shashfrankenstien/ArchieTiny/src/drivers/sh1106.asm

; this program interfaces with SH1106 OLED display over i2c

.equ OLED_ADDR,                 0b00111100              ; 0x3c
.equ OLED_WRITE_ADDR,           (OLED_ADDR << 1) | 0x00 ; 0x78
.equ OLED_READ_ADDR,            (OLED_ADDR << 1) | 0x01 ; 0x79

; control byte                                          ; if bit 8 is set, we can send 1 data byte after this
.equ OLED_WRITE_DATA,           0b11000000              ; if bit 7 is set, indicates that the next byte needs to be stored in memory
.equ OLED_WRITE_CMD,            0b10000000              ; if bit 7 is clear, the next byte will be a command

.equ OLED_WRITE_DATA_LIST,      0b01000000
.equ OLED_WRITE_CMD_LIST,       0b00000000

.equ OLED_READ_MOD_WRITE_START, 0xe0                    ; commands for read-modify-write operation
.equ OLED_READ_MOD_WRITE_END,   0xee                    ; see page 28 of sh1106 data sheet

; commands
.equ SET_DISPLY_OFF,         0xae                    ; 0b1010111x
.equ SET_DISPLY_ON,          0xaf                    ; where x is 1 for ON and 0 for OFF

.equ SET_PAGE_ADDRESS,       0xb0                    ; 0b10110xxx where xxx are page addresses 0 - 7
.equ SET_COLUMN_L,           0x00                    ; 0b0000xxxx where xxxx are column number low bits
.equ SET_COLUMN_H,           0x10                    ; 0b0001xxxx where xxxx are column number high bits

.equ SET_DISP_FREQ_MODE,     0xd5                    ; double command. use with DEFAULT_DISP_FREQ
.equ DEFAULT_DISP_FREQ,      0x50

.equ SET_COLOR_NORM,         0xa6                    ; normal = white fg, black bg
.equ SET_COLOR_INV,          0xa7                    ; inverted = black fg, white bg

.equ SET_COMM_SCAN_DIR_NORM, 0xc0                    ; normal = page numbers start on the end away from the i2c pinout
.equ SET_COMM_SCAN_DIR_INV,  0xc8                    ; inverted = page numbers start on the end closer to the i2c pinout

.equ SET_SEGMENT_REMAP_NORM, 0xa0                    ; column scanning direction left to right or right to left
.equ SET_SEGMENT_REMAP_INV,  0xa1                    ; reverse of SET_SEGMENT_REMAP_NORM

.equ SET_DISPLY_LINE_OFFSET, 0xd3                    ; set display offset (double byte command) - followed by a number betwee 0 - 63

.equ SET_DISPLY_START_LINE,  0x40                    ; set display start line: (0x40 - 0x7f) - ORed with a number betwee 0 - 63


.equ SET_CONTRAST_CMD,      0x81                     ; set contrast (double byte command) - followed by a number betwee 0 - 255



; SREG_OLED - oled status register (1)
;   - register holds 8 oled status flags
;      --------------------------------------------------------------------------------------------------------------
;      |  CNTRST3  |  CNTRST2  |  CNTRST1  |  CNTRST0  |  OLED_COLOR_INVERT  |  SCRL_PG2  |  SCRL_PG1  |  SCRL_PG0  |
;      --------------------------------------------------------------------------------------------------------------
;
; SCRL_PG[2:0] - display scroll page (bits 2:0)
;   - this is a 3 bit number indicating current page scroll position on the screen (0 - 7)
;   - text scrolling is performed 8 rows (1 page) at a time
;   - oled_set_cursor routine can use this to normalize column and row indexing to the user
;
; OLED_COLOR_INVERT (bit 3)
;   - this flag is used to implement software color inverted mode
;   - NOTE: this is different from SET_COLOR_INV, which is an oled device function to invert the entire screen
;   - if OLED_COLOR_INVERT is set, anything written through the oled routines will be inverted (1's complement using COM instruction)
;       if OLED_COLOR_INVERT is cleared, it writes without 1's complement
.equ    OLED_COLOR_INVERT,       3
;
; OLED contrast level - SREG_OLED[7:4] (CNTRST[3:0])
;   - location to store current contrast level set by oled_set_contrast

;
; --------------------------------------------------
.equ    OLED_MAX_COL,            127                        ; max column index (128 x 64)
.equ    OLED_MAX_PAGE,           7                          ; max page index (each page has 8 rows)
.equ    OLED_MAX_ROWS,           ((OLED_MAX_PAGE + 1) * 8)  ; each page has 8 rows. OLED_MAX_ROWS = number of pages * 8
; --------------------------------------------------


; initialize oled and set default settings
oled_init:
    push r16

    clr r16
    sts SREG_OLED, r16                         ; clear oled status register

    rcall i2c_do_stop_condition                ; call stop condition just in case (mostly not required)

    rcall oled_io_open_write_cmds

    ldi r16, SET_DISPLY_OFF                    ; turn on the display
    rcall i2c_send_byte
    ldi r16, SET_DISP_FREQ_MODE                ; set the display refresh rate (double command)
    rcall i2c_send_byte
    ldi r16, DEFAULT_DISP_FREQ
    rcall i2c_send_byte

    ; ; rotate oled 180 degrees by flipping both column and page scan directions
    ; ldi r16, SET_COMM_SCAN_DIR_INV             ; flip the screen
    ; rcall i2c_send_byte
    ; ldi r16, SET_SEGMENT_REMAP_INV             ; reverse the column scan direction
    ; rcall i2c_send_byte

    ldi r16, SET_DISPLY_LINE_OFFSET            ; set offset (different from scroll?)
    rcall i2c_send_byte
    ldi r16, 0
    rcall i2c_send_byte
    ldi r16, SET_DISPLY_START_LINE | 0         ; set scroll state to 0
    rcall i2c_send_byte

    ldi r16, SET_DISPLY_ON                     ; turn on the display
    rcall i2c_send_byte

    rcall oled_io_close
    rcall oled_clr_screen

    ldi r16, 5                                 ; default contrast = 5 (possible values 0 - 15)
    rcall oled_set_contrast

    pop r16
    ret



; ----------------- i2c IO wrappers ---------------

; use this routine to start a command list write transaction
; this routine modifies r16 so that it contains ACK in LSB
oled_io_open_write_cmds:
    rcall i2c_do_start_condition

    ldi r16, OLED_WRITE_ADDR                   ; i2c communication always starts with the address + read/write flag
    rcall i2c_send_byte

    ldi r16, OLED_WRITE_CMD_LIST               ; this control byte tells the display to expect a list of commands until stop condition
    rcall i2c_send_byte
    ret                                        ; return value r16 will contain ACK from last byte transfered


; use this routine to start a data list write transaction
; this routine modifies r16 so that it contains ACK in LSB
oled_io_open_write_data:
    rcall i2c_do_start_condition

    ldi r16, OLED_WRITE_ADDR                   ; i2c communication always starts with the address + read/write flag
    rcall i2c_send_byte

    ldi r16, OLED_WRITE_DATA_LIST              ; this tells the device to expect a list of data bytes until stop condition
    rcall i2c_send_byte
    ret                                        ; return value r16 will contain ACK from last byte transfered


; use this routine to start a data read transaction
; this routine modifies r16 so that it contains ACK in LSB
oled_io_open_read_data:
    rcall i2c_do_start_condition

    ldi r16, OLED_WRITE_ADDR                   ; oled retains the previous control byte indicating command or data
    rcall i2c_send_byte                        ; if command (OLED_WRITE_CMD - ex: setting the cursor), then the data read back will be the oled status flag
    ldi r16, OLED_WRITE_DATA                   ; so, first we need to write the command byte indicating we want to access data (OLED_WRITE_DATA)
    rcall i2c_send_byte

    rcall i2c_do_start_condition               ; then, we send a restart event after which we will be able to read display RAM data

    ldi r16, OLED_READ_ADDR                    ; i2c communication to read
    rcall i2c_send_byte

    rcall i2c_read_byte_ack                    ; perform dummy read per sh1106 docs
    ret


oled_io_close:
    rcall i2c_do_stop_condition
    ret



; ----------------- read-modify-write wrappers ---------------

oled_read_mod_write_start:
    rcall i2c_do_start_condition

    ldi r16, OLED_WRITE_ADDR                   ; i2c communication always starts with the address + read/write flag
    rcall i2c_send_byte

    ldi r16, OLED_WRITE_CMD
    rcall i2c_send_byte

    ldi r16, OLED_READ_MOD_WRITE_START
    rcall i2c_send_byte

    rcall i2c_do_stop_condition

    ret



oled_read_mod_write_end:
    rcall i2c_do_start_condition

    ldi r16, OLED_WRITE_ADDR                   ; i2c communication always starts with the address + read/write flag
    rcall i2c_send_byte

    ldi r16, OLED_WRITE_CMD
    rcall i2c_send_byte

    ldi r16, OLED_READ_MOD_WRITE_END
    rcall i2c_send_byte

    rcall i2c_do_stop_condition
    ret



; -------------- SREG_OLED wrappers ----------------

oled_color_inv_start:
    push r16
    lds r16, SREG_OLED
    sbr r16, (1 << OLED_COLOR_INVERT)        ; set to invert color
    sts SREG_OLED, r16
    pop r16
    ret


oled_color_inv_stop:
    push r16
    lds r16, SREG_OLED
    cbr r16, (1 << OLED_COLOR_INVERT)        ; set to normal color
    sts SREG_OLED, r16
    pop r16
    ret
; -------------------------------------------------



; oled_set_cursor takes
;   - r16 - page address
;   - r17 - column address
; performs set page and set column address operations
oled_set_cursor:
    .irp param,16,17,18,19
        push r\param
    .endr
    mov r19, r16                               ; store page number for later

    inc r17
    inc r17                                    ; screen is somehow offset by 2 columns ?? :/
                                               ; In SH1106 driver, 128x64 OLED is centered within the 132x64 ram,
                                               ;    that means pixel (2,0) in ram is pixel (0,0) on the display
    mov r18, r17
    swap r18
    andi r18, 0x0f                             ; keep high nibble of column address by swapping nibbles + andi 0x0f
    ori r18, SET_COLUMN_H                      ; set column start addr high nibble

    andi r17, 0x0f                             ; keep low nibble of column address
    ori r17, SET_COLUMN_L                      ; set column start addr low nibble

    rcall oled_io_open_write_cmds

    mov r16, r19                               ; get required page number
    ori r16, SET_PAGE_ADDRESS                  ; OR with SET_PAGE_ADDRESS cmd
    rcall i2c_send_byte

    ; set cursor to precomputed column low and high commands saved in r17 and r18
    mov r16, r17
    rcall i2c_send_byte
    mov r16, r18
    rcall i2c_send_byte

    rcall oled_io_close

    .irp param,19,18,17,16
        pop r\param
    .endr
    ret


; oled_set_relative_cursor takes
;   - r16 - page address
;   - r17 - column address
; performs set page and set column address operations
; not affected by current page scroll position SCRL_PG[2:0] in SREG_OLED
oled_set_relative_cursor:
    push r16
    push r18

    lds r18, SREG_OLED                         ; load SREG_OLED and get current scroll position
    add r16, r18                               ; relative page scroll position = (cur + req) & 0b00000111
    andi r16, 0b00000111
    rcall oled_set_cursor

    pop r18
    pop r16
    ret



; scrolls screen down by 8 rows since a page is 8 rows high (1 page)
; this method wipes the top row first before scrolling, leaving a new blank line at the bottom
oled_scroll_page_down:
    push r16
    push r17

    ; wipe top row
    clr r16
    clr r17
    rcall oled_wipe_eol

    ; perform scroll
    lds r16, SREG_OLED                         ; load SREG_OLED and get current scroll position
    mov r17, r16
    inc r16
    andi r16, 0b00000111                       ; keep only lower 3 bits in case of overflow (0 - 7)

    andi r17, 0b11111000                       ; keep higher 5 bits from current SREG_OLED
    or r17, r16
    sts SREG_OLED, r17                         ; update SREG_OLED with new scroll position

    ldi r17, 8
    rcall mul8                                 ; multiply r16 by 8 to get scroll position in rows (0 - 63). LSB of result is returned in r16
    andi r16, 0b00111111                       ; keep only lower 6 bits in case of overflow (0 - 63)
    mov r17, r16                               ; save new scroll position in r17

    rcall oled_io_open_write_cmds
    mov r16, r17                               ; reload r16 as oled_io_open_write_cmds modifies this register
    ori r16, SET_DISPLY_START_LINE
    rcall i2c_send_byte
    rcall oled_io_close

    pop r17
    pop r16
    ret



; scrolls screen up by 8 rows since a page is 8 rows high (1 page)
; this method wipes the bottom row first before scrolling, leaving a new blank line at the top
oled_scroll_page_up:
    push r16
    push r17

    ; wipe bottom row
    ldi r16, OLED_MAX_PAGE
    clr r17
    rcall oled_wipe_eol

    ; perform scroll
    lds r16, SREG_OLED                         ; load SREG_OLED and get current scroll position
    mov r17, r16
    dec r16
    andi r16, 0b00000111                       ; keep only lower 3 bits in case of overflow (0 - 7)

    andi r17, 0b11111000                       ; keep higher 5 bits from current SREG_OLED
    or r17, r16
    sts SREG_OLED, r17                         ; update SREG_OLED with new scroll position

    ldi r17, 8
    rcall mul8                                 ; multiply r16 by 8 to get scroll position in rows (0 - 63). LSB of result is returned in r16
    andi r16, 0b00111111                       ; keep only lower 6 bits in case of overflow (0 - 63)
    mov r17, r16                               ; save new scroll position in r17

    rcall oled_io_open_write_cmds
    mov r16, r17                               ; reload r16 as oled_io_open_write_cmds modifies this register
    ori r16, SET_DISPLY_START_LINE
    rcall i2c_send_byte
    rcall oled_io_close

    pop r17
    pop r16
    ret


; resets oled scroll position
oled_scroll_page_reset:
    push r16

    lds r16, SREG_OLED                         ; load SREG_OLED and get current scroll position
    cbr r16, 0b00000111                        ; set scroll position to 0
    sts SREG_OLED, r16                         ; update SREG_OLED

    rcall oled_io_open_write_cmds
    ldi r16, SET_DISPLY_START_LINE | 0         ; set scroll position to 0
    rcall i2c_send_byte
    rcall oled_io_close

    pop r16
    ret


; oled_set_contrast takes contrast value in r16
;   - this routine scales the value down to 16 steps (takes 0 to 15 in r16)
oled_set_contrast:
    push r16
    push r17

    andi r16, 0b00001111                        ; only keep low 4 bits (0 to 15)

    lds r17, SREG_OLED                          ; read current SREG_OLED
    andi r17, 0b00001111                        ; only keep low 4 bits and update high 4 bits with contrast value
    swap r17
    or r17, r16
    swap r17
    sts SREG_OLED, r17                          ; update SREG_OLED

    ldi r17, 16
    rcall mul8                                  ; scale up: 0 to 15 => 0 to 255

    cpi r16, 1                                  ; minimum allowed value is 1 (this will be used if output value is 0)
    brsh _oled_set_contrast_ok
    ldi r16, 1
_oled_set_contrast_ok:
    push r16
    rcall oled_io_open_write_cmds
    ldi r16, SET_CONTRAST_CMD
    rcall i2c_send_byte
    pop r16
    rcall i2c_send_byte
    rcall oled_io_close

    pop r17
    pop r16
    ret

; -------------------------------------------------

; write all zeros onto oled
; also reset scroll position
oled_clr_screen:
    .irp param,16,17,18,19,20
        push r\param
    .endr

    clr r16                                    ; fill byte = 0x00 (all 0s)
    clr r17                                    ; x1 = 0
    ldi r18, OLED_MAX_COL                      ; x2 = OLED_MAX_COL
    clr r19                                    ; y2 = 0
    ldi r20, OLED_MAX_ROWS                     ; y2 = OLED_MAX_ROWS (64 on the regular oled)
    rcall oled_fill_rect              ; fill oled with data in r16

    rcall oled_scroll_page_reset               ; reset scroll position

    .irp param,20,19,18,17,16
        pop r\param
    .endr
    ret



; 'oled_wipe_eol' takes
;   - r16 - page address
;   - r17 - column address
; sets the cursor to the required location
; writes 0s till end of line from current column (r17)
; returns after resetting the cursor to the right location
oled_wipe_eol:
    push r16
    push r17

    rcall oled_set_relative_cursor             ; set cursor initially
    rcall oled_io_open_write_data

_next_wipe_column:
    clr r16
    rcall i2c_send_byte                        ; i2c_send_byte modifies r16, so we need to reload r16 at every iteration
    inc r17
    cpi r17, OLED_MAX_COL + 1
    brne _next_wipe_column

    rcall oled_io_close                        ; finished writing a page

    pop r17
    pop r16
    rcall oled_set_relative_cursor             ; finally set cursor to desired page (r16) and column (r17)
    ret


; --------------------------------------------------


; oled_fill_page_row takes 3 coordinates - x1, x2, y
; it will fill page y between x1 and x2 columns with the fill byte in r16
; input registers -
;   r16 - byte to fill
;   r17 - x1
;   r18 - x2
;   r19 - y         ; row (page) address 0 to 7
oled_fill_page_row:
    .irp param,17,18,19,20
        push r\param
    .endr

    inc r18                                    ; increment x2 so that we can break the loop once x1 overflows original x2
    mov r20, r16                               ; save away page fill byte till later because we need r16 for other stuff
    mov r16, r19
    rcall oled_set_cursor                      ; set cursor to start writing data

    rcall oled_io_open_write_data
_fill_page_next_column:                                  ; iterate columns x1 to x2
    mov r16, r20                               ; load back the fill byte that was originally saved away
    rcall i2c_send_byte                        ; i2c_send_byte modifies r16, so we need to reload r16 at every iteration
    inc r17
    cp r17, r18
    brne _fill_page_next_column

    rcall oled_io_close                        ; finished writing a page

    .irp param,20,19,18,17
        pop r\param
    .endr
    ret                                        ; return value r16 will contain ACK from last byte transfered



; oled_invert_inplace_relative_page_row takes 3 coordinates - x1, x2, y
; it will invert all bytes of page y between x1 and x2 columns
; input registers follow oled_fill_page_row convention -
;   r17 - x1
;   r18 - x2
;   r19 - y         ; row (page) address 0 to 7
oled_invert_inplace_relative_page_row:
    .irp param,16,17,18,19,20
        push r\param
    .endr

    inc r18                                    ; increment x2 so that we can break the loop once x1 overflows original x2
    mov r16, r19
    rcall oled_set_relative_cursor             ; set cursor to start writing data

    rcall oled_read_mod_write_start
_invert_inplace_next_column:
    rcall oled_io_open_read_data
    rcall i2c_read_byte_nack
    mov r20, r16
    rcall oled_io_close

    rcall oled_io_open_write_data
    mov r16, r20
    com r16
    rcall i2c_send_byte
    rcall oled_io_close
    inc r17
    cp r17, r18
    brne _invert_inplace_next_column

    rcall oled_read_mod_write_end

    .irp param,20,19,18,17,16
        pop r\param
    .endr
    ret






; oled_fill_rect takes 4 coordinates - x1, x2, y1, y2
; it will fill the rectangle between (x1,y1) (x1,y2) (x2,y1) (x2,y2)
; input registers -
;   r16 - byte to fill
;   r17 - x1
;   r18 - x2
;   r19 - y1
;   r20 - y2
;
; so
;   x1 and x2 indicate column addresses
;   y1 and y2 indicate actual row addresses between 0 and 63 (pixel resolution)
;
; handling y axis - convert 0 - 63 into page addr (0 - 7) and bit addr (0 - 7)
;   - this can be done by dividing the y value by 8. quotient will be page addr and remainder will be bit addr
;
; first, we will fill the pages associated with y1 and y2 with corresponding bit addr masked fill byte
; then, we will check if there are pages between y1 and y2 that needs filling, and fill those with the raw fill byte
oled_fill_rect:                               ; fill rect on screen with value in r16
                                               ; r16 through r20 are inputs. calling routine should push and pop these
    push r22
    push r23
    push r24
    push r25

    ; pre calc some stuff
    mov r22, r16                               ; save away page fill byte till later because we need r16 for other stuff
    lds r16, SREG_OLED
    sbrc r16, OLED_COLOR_INVERT                ; check if needs to be inverted
    com r22                                    ; invert!

    mov r23, r17                               ; save away x1 as we need r17 for div8

    ;  ------------------ deal with y1 -----------------------
    mov r16, r19
    ldi r17, 8
    rcall div8
    mov r19, r16                               ; move y1 page number into r19
    mov r16, r22                               ; load back the fill byte that was originally saved away

    tst r17
    breq _rect_page_0_fill_mask_done

    clc                                        ; clear carry flag
    ldi r24, 0xff
_rect_page_0_fill_mask:
    rol r24                                    ; bring in carry to bit 0
    and r16, r24                               ; knock off one LSB at a time using rol+and
    dec r17
    brne _rect_page_0_fill_mask

_rect_page_0_fill_mask_done:
    mov r17, r23                               ; load back x1
    rcall oled_fill_page_row
    mov r25, r19                               ; save away y1 page number for later

    ;  ------------------ deal with y2 -----------------------
    mov r16, r20
    ldi r17, 8
    rcall div8
    mov r19, r16                               ; move y2 page number into r19

    tst r17
    breq _rect_page_n_done

    ldi r16, 8
    sub r16, r17
    mov r17, r16

    mov r16, r22                               ; load back the fill byte that was originally saved away
    clc                                        ; clear carry flag
    ldi r24, 0xff
_rect_page_n_fill_mask:
    ror r24                                    ; bring in carry to bit 7
    and r16, r24                               ; knock off one MSB at a time using ror+and
    dec r17
    brne _rect_page_n_fill_mask

    mov r17, r23                               ; load back x1
    rcall oled_fill_page_row

_rect_page_n_done:
    mov r20, r19                               ; put y2 page number in r20
    mov r19, r25                               ; put y1 page number in r19
    ; ------------------------------------------------------------

    sub r20, r19                               ; subtract y1 from y2. if result is same or higher than 2, we need to fill intermediate pages
    cpi r20, 2
    brlo _rect_done

    dec r20                                    ; iterator for intermediate pages
    inc r19                                    ; start from the second page since first one is already handled (y1)

_rect_next_page2:                              ; iterate intermediate pages
    mov r16, r22                               ; load back the fill byte that was originally saved away
    rcall oled_fill_page_row
    inc r19
    dec r20
    brne _rect_next_page2

_rect_done:
    pop r25
    pop r24
    pop r23
    pop r22                                    ; r16 through r20 are inputs. calling routine should push and pop these
    ret                                        ; return value r16 will contain ACK from last byte transfered




; oled_draw_h_line_overlay takes 2 coordinates - x1, x2 and y
; it will draw a vertical line between x1 and x2 on row y
; input registers follow oled_fill_rect convention -
;   r16 - y
;   r17 - x1
;   r18 - x2
oled_draw_h_line_overlay:                      ; draw a horizontal line on screen without distorting existing pixels (*much)
    .irp param,16,17,18,19,20,21
        push r\param
    .endr

    mov r19, r16
    mov r20, r17

    ldi r17, 8
    rcall div8
    mov r21, r17
    mov r17, r20

    sec                                        ; set carry flag
    clr r20
    inc r21                                    ; increment r21 so that we can break once it reaches 0
_draw_h_line_bit_mask:
    rol r20                                    ; rotate in carry bit
    dec r21
    brne _draw_h_line_bit_mask

    rcall oled_set_relative_cursor
    rcall oled_read_mod_write_start
_draw_h_line_next_column:
    rcall oled_io_open_read_data
    rcall i2c_read_byte_nack
    mov r21, r16
    rcall oled_io_close

    or r21, r20

    rcall oled_io_open_write_data
    mov r16, r21
    rcall i2c_send_byte
    rcall oled_io_close
    inc r17
    cp r17, r18
    brne _draw_h_line_next_column

    rcall oled_read_mod_write_end

    .irp param,21,20,19,18,17,16
        pop r\param
    .endr
    ret


; ; oled_draw_line_overlay takes 4 coordinates - x1, x2, y1, y2
; ; it will fill the rectangle between (x1,y1) (x1,y2) (x2,y1) (x2,y2)
; ; input registers follow oled_fill_rect convention -
; ;   r17 - x1
; ;   r18 - x2
; ;   r19 - y1
; ;   r20 - y2
; ;
; oled_draw_line_overlay:               ; draw a line on screen without distorting existing pixels (*much)

;     mov r21, r20
;     sub r21, r19                              ; r21 = y2 - y1

;     mov r22, r18
;     sub r22, r17                              ; r22 = x2 - x1

;     mov r16, r21
;     mov r21, r17
;     mov r17, r22
;     rcall div8                                ; r16 (quotient), r17 (remainder) => (y2 - y1) / (x2 - x1). aka 'm' or slope

; --------------------------------------------------



; oled_io_put_char depends on a font being included. it will expect
;   - a label 'font_lut' that contains the lookup table for characters
;   - FONT_WIDTH constant which indicates how many bytes need to be written per character
;   - FONT_OFFSET constant which indicates the first ascii charater in the lookup table
;           consequent characters can be reached by incrementing by FONT_WIDTH
;
; it take one character ascii value in r16
; to write the character, we need to find the index of the character in font_lut
;   - index = addr of font_lut + ((r16 - FONT_OFFSET) * FONT_WIDTH)
;
; oled_io_put_char assumes that start condition has been signaled and cursor address is set before being called
; it also expects that the oled is in OLED_WRITE_DATA_LIST mode
; - these conditions can be met by just calling oled_io_open_write_data before, and oled_io_close after oled_io_put_char
oled_io_put_char:
    .irp param,17,18,19,30,31
        push r\param
    .endr
    in r19, SREG
    lds r18, SREG_OLED

    ldi r31, hi8(font_lut)          ; initialize Z-pointer to the start of the font lookup table
    ldi r30, lo8(font_lut)

    subi r16, FONT_OFFSET           ; (r16 - FONT_OFFSET) * FONT_WIDTH
    ldi r17, FONT_WIDTH
    rcall mul8                      ; output is stored in r17:r16 (character index)

    add r30, r16                    ; add the character index to Z pointer
    adc r31, r17                    ; add the character index to Z pointer

    ldi r17, FONT_WIDTH             ; load loop counter
_oled_io_put_char_next_byte:
    lpm r16, Z+                     ; load constant from flash
                                    ; memory pointed to by Z (r31:r30)
    sbrc r18, OLED_COLOR_INVERT     ; check if needs to be inverted
    com r16                         ; invert!
    rcall i2c_send_byte
    dec r17
    brne _oled_io_put_char_next_byte

    out SREG, r19
    .irp param,31,30,19,18,17
        pop r\param
    .endr
    ret                             ; return value r16 will contain ACK from last byte transfered




; oled_io_put_icon depends on a custom icon set being included. it will expect
;   - a label 'icon_lut' that contains the lookup table for icons
;   - ICON_WIDTH constant which indicates how many bytes need to be written per icon
;           consequent icons can be reached by incrementing by ICON_WIDTH
;
; it take one icon value in r16
; to write the icon, we need to find the index of the icon in icon_lut
;   - index = addr of icon_lut + (r16 * ICON_WIDTH)
;
; oled_io_put_icon assumes that start condition has been signaled and cursor address is set before being called
; it also expects that the oled is in OLED_WRITE_DATA_LIST mode
; - these conditions can be met by just calling oled_io_open_write_data before, and oled_io_close after oled_io_put_icon
oled_io_put_icon:
    .irp param,17,18,19,30,31
        push r\param
    .endr
    in r19, SREG
    lds r18, SREG_OLED

    ldi r31, hi8(icon_lut)          ; initialize Z-pointer to the start of the icon lookup table
    ldi r30, lo8(icon_lut)

    ldi r17, ICON_WIDTH             ; r16 * ICON_WIDTH
    rcall mul8                      ; output is stored in r17:r16 (icon index)

    add r30, r16                    ; add the icon index to Z pointer
    adc r31, r17                    ; add the icon index to Z pointer

    ldi r17, ICON_WIDTH             ; load loop counter
_oled_io_put_icon_next_byte:
    lpm r16, Z+                     ; load constant from flash
                                    ; memory pointed to by Z (r31:r30)
    sbrc r18, OLED_COLOR_INVERT     ; check if needs to be inverted
    com r16                         ; invert!
    rcall i2c_send_byte
    dec r17
    brne _oled_io_put_icon_next_byte

    out SREG, r19
    .irp param,31,30,19,18,17
        pop r\param
    .endr
    ret                             ; return value r16 will contain ACK from last byte transfered




; oled_print_flash reads string from flash and writes to oled
; it expects
;   - Z pointer set at the start of the string
;   - String HAS to be null-terminated. routine exits if \0 (null) is encountered
oled_print_flash:
    push r17
    push r18
    in r18, SREG

    clr r17
    rcall oled_io_open_write_data   ; this tells the device to expect a list of data bytes until stop condition

_print_flash_next_char:
    lpm r16, Z+                     ; load character from flash memory
                                    ; memory pointed to by Z (r31:r30)
    cpi r16, 0
    breq _print_flash_done
    rcall oled_io_put_char
    inc r17
    rjmp _print_flash_next_char

_print_flash_done:
    rcall oled_io_close

    mov r16, r17                    ; return value r16 will contain number of characters written
    out SREG, r18
    pop r18
    pop r17
    ret



; ; oled_print_binary_digits converts r16 to is and 0s and writes to oled
; oled_print_binary_digits:
;     .irp param,18,19,20
;         push r\param
;     .endr
;     mov r18, r16                               ; save r16 for later

;     rcall oled_io_open_write_data               ; this tells the device to expect a list of data bytes until stop condition

;     ldi r19, 8
;     ldi r20, 48
; _next_bin_char:
;     clr r16
;     lsl r18
;     rol r16
;     add r16, r20
;     rcall oled_io_put_char
;     dec r19
;     brne _next_bin_char

;     rcall oled_io_close

;     .irp param,20,19,18
;         pop r\param
;     .endr
;     ret                             ; return value r16 will contain ACK from last byte transfered




internal_oled_low_nibble_to_hex_char:
    push r17
    andi r16, 0b00001111                    ; only lower nibble
    cpi r16, 10
    brsh _hex_ge_10
    ldi r17, '0'
    rjmp _hex_write_low
_hex_ge_10:
    ldi r17, 'a'
    subi r16, 10
_hex_write_low:
    add r16, r17
    pop r17
    ret


; oled_print_hex_digits converts r16 to hex and writes to oled
oled_print_hex_digits:
    .irp param,17,18,20
        push r\param
    .endr
    in r17, SREG
    mov r18, r16                               ; save r16 for later

    rcall oled_io_open_write_data               ; this tells the device to expect a list of data bytes until stop condition

    mov r16, r18
    swap r16
    rcall internal_oled_low_nibble_to_hex_char
    rcall oled_io_put_char

    mov r16, r18
    rcall internal_oled_low_nibble_to_hex_char
    rcall oled_io_put_char

    rcall oled_io_close

    out SREG, r17
    .irp param,20,18,17
        pop r\param
    .endr
    ret                             ; return value r16 will contain ACK from last byte transfered
